Jaans/Voron-Printer-Mods/Bouncy-Mouse/Images/Skirt_250.png

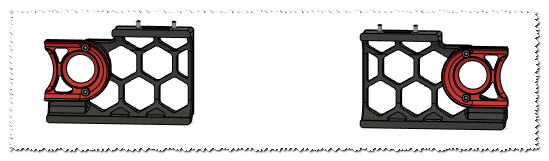
Bouncy-Mouse/Images/Skirt_250.png
