Jaans/Voron-Printer-Mods/Bouncy-Mouse/Images/Skirt_300.png

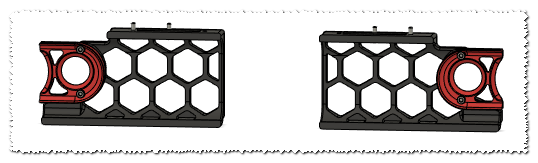
Bouncy-Mouse/Images/Skirt_300.png
