Jaans/Voron-Printer-Mods/Bouncy-Mouse/Images/Skirt_350.png

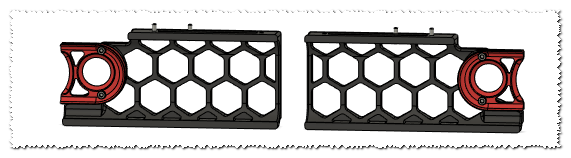
Bouncy-Mouse/Images/Skirt_350.png
