Jaans/Voron-Printer-Mods/Bouncy-Mouse/STL/cover-arrow-vertical-dot-dot v2.stl

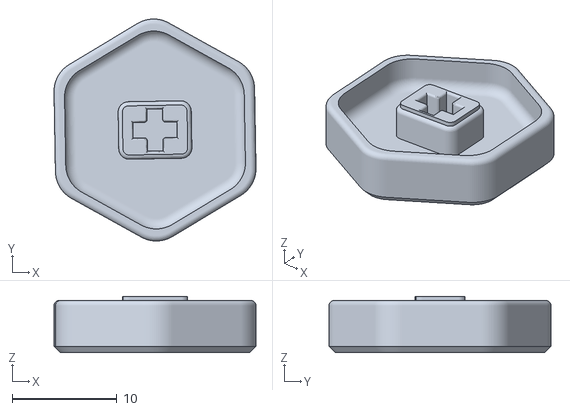
[picture p49: CAD file, 2022-12-21]
Bouncy-Mouse/STL/cover-arrow-vertical-dot-dot v2.stl
19.3 x 21.2 x 5.40
